kleinesfilmroellchen/MusikWecker/LUTMath.cpp

#include "LUTMath.h"
#include "Definitions.h"

static const float lut[257] PROGMEM = {
	0.0000000000, 0.0061358846, 0.0122715383, 0.0184067299,
	0.0245412285, 0.0306748032, 0.0368072229, 0.0429382569,
	0.0490676743, 0.0551952443, 0.0613207363, 0.0674439196,
	0.0735645636, 0.0796824380, 0.0857973123, 0.0919089565,
	0.0980171403, 0.1041216339, 0.1102222073, 0.1163186309,
	0.1224106752, 0.1284981108, 0.1345807085, 0.1406582393,
	0.1467304745, 0.1527971853, 0.1588581433, 0.1649131205,
	0.1709618888, 0.1770042204, 0.1830398880, 0.1890686641,
	0.1950903220, 0.2011046348, 0.2071113762, 0.2131103199,
	0.2191012402, 0.2250839114, 0.2310581083, 0.2370236060,
	0.2429801799, 0.2489276057, 0.2548656596, 0.2607941179,
	0.2667127575, 0.2726213554, 0.2785196894, 0.2844075372,
	0.2902846773, 0.2961508882, 0.3020059493, 0.3078496400,
	0.3136817404, 0.3195020308, 0.3253102922, 0.3311063058,
	0.3368898534, 0.3426607173, 0.3484186802, 0.3541635254,
	0.3598950365, 0.3656129978, 0.3713171940, 0.3770074102,
	0.3826834324, 0.3883450467, 0.3939920401, 0.3996241998,
	0.4052413140, 0.4108431711, 0.4164295601, 0.4220002708,
	0.4275550934, 0.4330938189, 0.4386162385, 0.4441221446,
	0.4496113297, 0.4550835871, 0.4605387110, 0.4659764958,
	0.4713967368, 0.4767992301, 0.4821837721, 0.4875501601,
	0.4928981922, 0.4982276670, 0.5035383837, 0.5088301425,
	0.5141027442, 0.5193559902, 0.5245896827, 0.5298036247,
	0.5349976199, 0.5401714727, 0.5453249884, 0.5504579729,
	0.5555702330, 0.5606615762, 0.5657318108, 0.5707807459,
	0.5758081914, 0.5808139581, 0.5857978575, 0.5907597019,
	0.5956993045, 0.6006164794, 0.6055110414, 0.6103828063,
	0.6152315906, 0.6200572118, 0.6248594881, 0.6296382389,
	0.6343932842, 0.6391244449, 0.6438315429, 0.6485144010,
	0.6531728430, 0.6578066933, 0.6624157776, 0.6669999223,
	0.6715589548, 0.6760927036, 0.6806009978, 0.6850836678,
	0.6895405447, 0.6939714609, 0.6983762494, 0.7027547445,
	0.7071067812, 0.7114321957, 0.7157308253, 0.7200025080,
	0.7242470830, 0.7284643904, 0.7326542717, 0.7368165689,
	0.7409511254, 0.7450577854, 0.7491363945, 0.7531867990,
	0.7572088465, 0.7612023855, 0.7651672656, 0.7691033376,
	0.7730104534, 0.7768884657, 0.7807372286, 0.7845565972,
	0.7883464276, 0.7921065773, 0.7958369046, 0.7995372691,
	0.8032075315, 0.8068475535, 0.8104571983, 0.8140363297,
	0.8175848132, 0.8211025150, 0.8245893028, 0.8280450453,
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
};

constexpr size_t LUT_SIZE = 256 * 4;
constexpr size_t PI_INDEX = LUT_SIZE / 2;

constexpr int ITERATIONS = 20000;

// https://stackoverflow.com/questions/11630321/why-does-c-output-negative-numbers-when-using-modulo
// fuck c++
inline int mod(int a, int b)
{
	int ret = a % b;
	return ret >= 0 ? ret : ret + b;
}

float sin_indexed(int real_index)
{
	auto value = 0.0f;
	if (real_index < PI_INDEX / 2) {
		// Serial.printf("first quadrant ");
		value = lut[real_index];
	} else if (real_index < PI_INDEX) {
		// Serial.printf("second quadrant %d ", PI_INDEX - real_index);
		value = lut[PI_INDEX - real_index];
	} else if (real_index < (PI_INDEX * 3 / 2)) {
		// Serial.printf("third quadrant %d ", real_index - PI_INDEX);
		value = -lut[real_index - PI_INDEX];
	} else {
		// Serial.printf("fourth quadrant %d ", 2 * PI_INDEX - real_index);
		value = -lut[2 * PI_INDEX - real_index];
	}
	return value;
}

constexpr float FLOAT_INT_FACTOR = LUT_SIZE / PI_FACTOR<2, 1>;

float sin_lut(float angle)
{
	const float index = angle * FLOAT_INT_FACTOR;
	const int real_index = mod(static_cast<int>(index), LUT_SIZE);
	// Serial.printf("%f -> %d ", angle, real_index);
	return sin_indexed(real_index);
}

float cos_lut(float angle)
{
	const float index = angle * FLOAT_INT_FACTOR;
	const int real_index = mod(static_cast<int>(index) + (LUT_SIZE / 4), LUT_SIZE);
	return sin_indexed(real_index);
}
