kleinesfilmroellchen/MusikWecker/EnumBits.h

/*
 * Copyright (c) 2021, Brian Gianforcaro <bgianf@serenityos.org>
 *
 * SPDX-License-Identifier: BSD-2-Clause
 */

#pragma once

#include <type_traits>

// Enables bitwise operators for the specified Enum type.
//
#define AK_ENUM_BITWISE_OPERATORS(Enum) \
	_AK_ENUM_BITWISE_OPERATORS_INTERNAL(Enum, )

#define _AK_ENUM_BITWISE_OPERATORS_INTERNAL(Enum, Prefix)                  \
                                                                           \
	[[nodiscard]] Prefix constexpr Enum operator|(Enum lhs, Enum rhs)      \
	{                                                                      \
		using Type = std::underlying_type<Enum>::type;                           \
		return static_cast<Enum>(                                          \
			static_cast<Type>(lhs) | static_cast<Type>(rhs));              \
	}                                                                      \
                                                                           \
	[[nodiscard]] Prefix constexpr Enum operator&(Enum lhs, Enum rhs)      \
	{                                                                      \
		using Type = std::underlying_type<Enum>::type;                           \
		return static_cast<Enum>(                                          \
			static_cast<Type>(lhs) & static_cast<Type>(rhs));              \
	}                                                                      \
                                                                           \
	[[nodiscard]] Prefix constexpr Enum operator^(Enum lhs, Enum rhs)      \
	{                                                                      \
		using Type = std::underlying_type<Enum>::type;                           \
		return static_cast<Enum>(                                          \
			static_cast<Type>(lhs) ^ static_cast<Type>(rhs));              \
	}                                                                      \
                                                                           \
	[[nodiscard]] Prefix constexpr Enum operator~(Enum rhs)                \
	{                                                                      \
		using Type = std::underlying_type<Enum>::type;                           \
		return static_cast<Enum>(                                          \
			~static_cast<Type>(rhs));                                      \
	}                                                                      \
                                                                           \
	Prefix constexpr Enum& operator|=(Enum& lhs, Enum rhs)                 \
	{                                                                      \
		using Type = std::underlying_type<Enum>::type;                           \
		lhs = static_cast<Enum>(                                           \
			static_cast<Type>(lhs) | static_cast<Type>(rhs));              \
		return lhs;                                                        \
	}                                                                      \
                                                                           \
	Prefix constexpr Enum& operator&=(Enum& lhs, Enum rhs)                 \
	{                                                                      \
		using Type = std::underlying_type<Enum>::type;                           \
		lhs = static_cast<Enum>(                                           \
			static_cast<Type>(lhs) & static_cast<Type>(rhs));              \
		return lhs;                                                        \
	}                                                                      \
                                                                           \
	Prefix constexpr Enum& operator^=(Enum& lhs, Enum rhs)                 \
	{                                                                      \
		using Type = std::underlying_type<Enum>::type;                           \
		lhs = static_cast<Enum>(                                           \
			static_cast<Type>(lhs) ^ static_cast<Type>(rhs));              \
		return lhs;                                                        \
	}                                                                      \
                                                                           \
	Prefix constexpr bool has_flag(Enum value, Enum mask)                  \
	{                                                                      \
		using Type = std::underlying_type<Enum>::type;                           \
		return static_cast<Type>(value & mask) == static_cast<Type>(mask); \
	}                                                                      \
                                                                           \
	Prefix constexpr bool has_any_flag(Enum value, Enum mask)              \
	{                                                                      \
		using Type = std::underlying_type<Enum>::type;                           \
		return static_cast<Type>(value & mask) != 0;                       \
	}
